COREi64/The-Phantom/Miniature Phantom by Tommi_nrw/C64 Userport Connections Reference.jpg

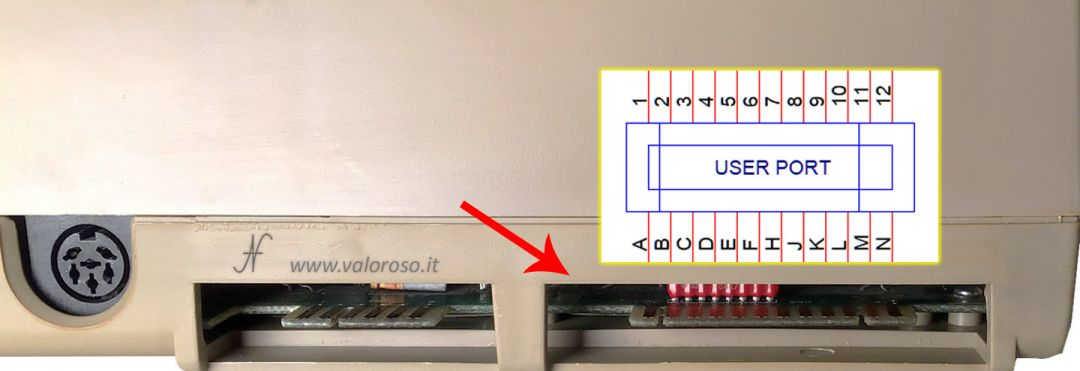
Miniature Phantom by Tommi_nrw/C64 Userport Connections Reference.jpg
