COREi64/The-Phantom/Miniature Phantom by Tommi_nrw/connections.jpg

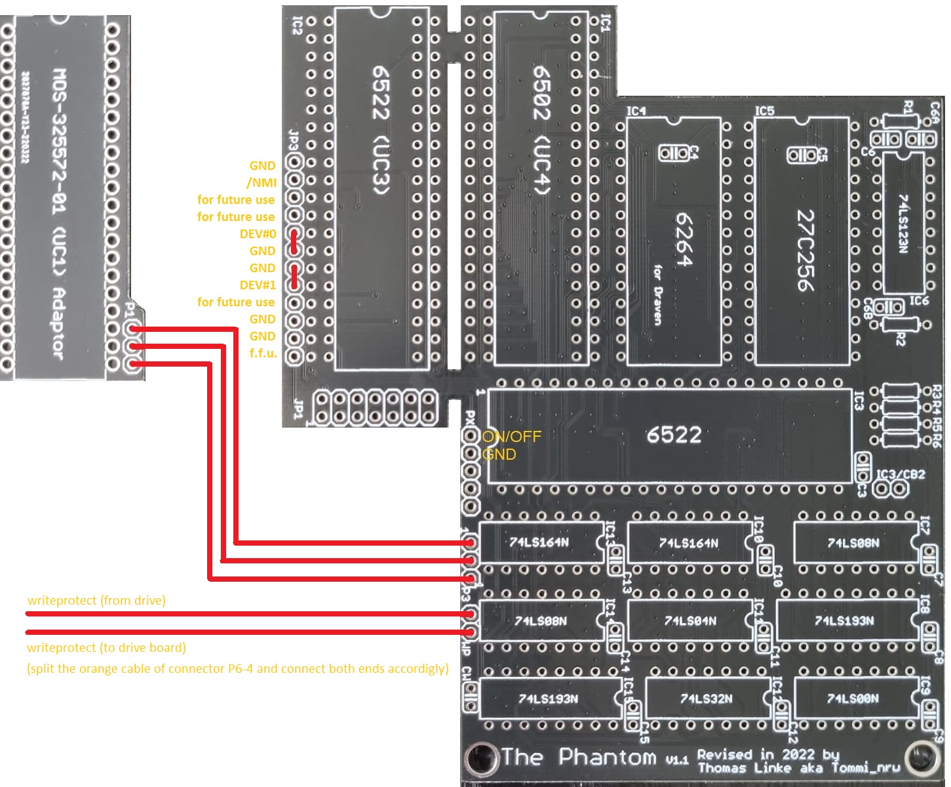
Miniature Phantom by Tommi_nrw/connections.jpg
