COREi64/The-Phantom/Miniature Phantom by Tommi_nrw/Gatearray-Adaptor.png

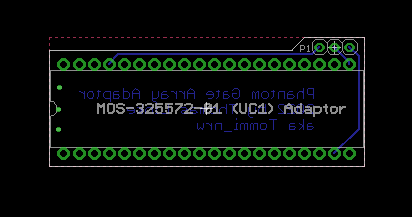
Miniature Phantom by Tommi_nrw/Gatearray-Adaptor.png
