COREi64/The-Phantom/Miniature Phantom by Tommi_nrw/Main PCB.png

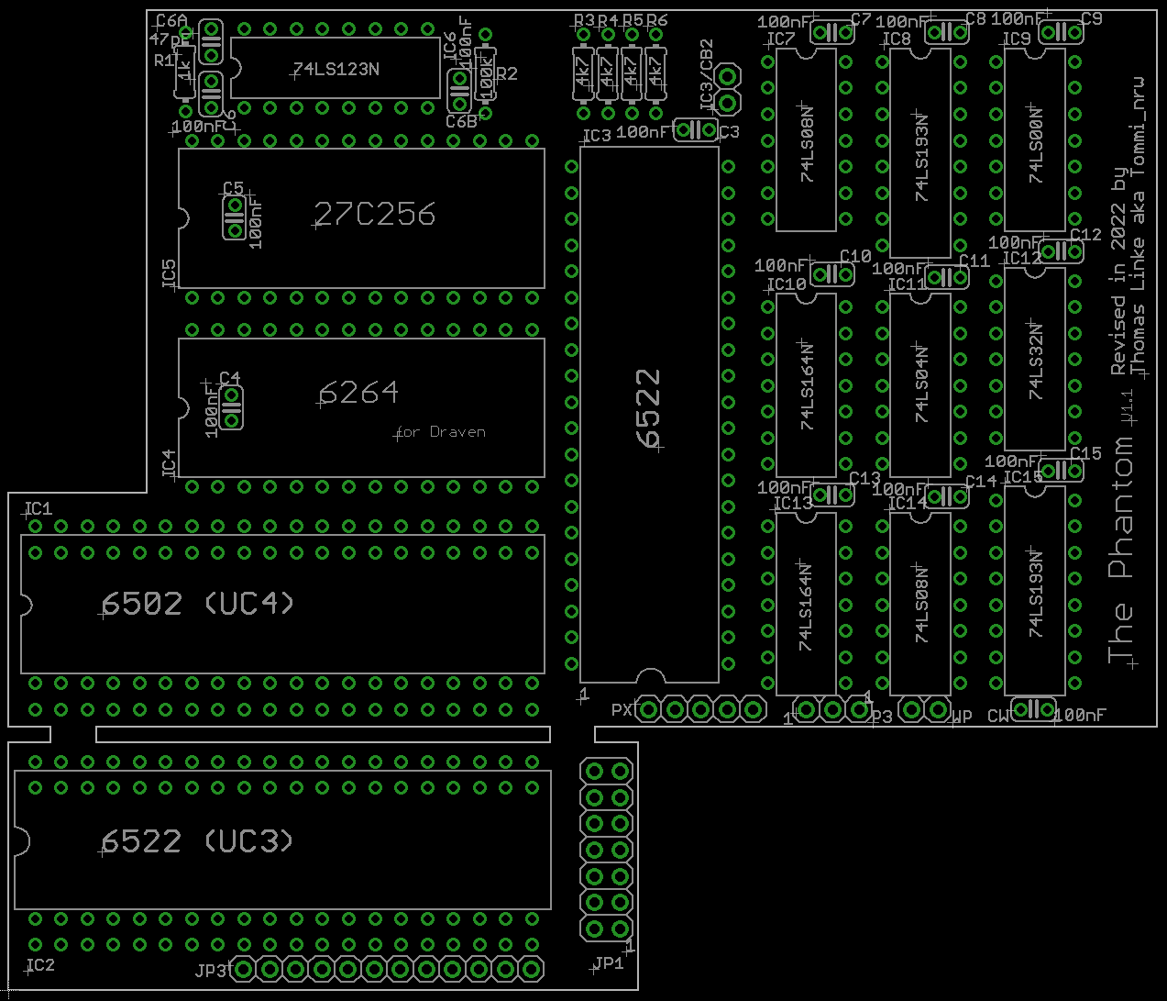
Miniature Phantom by Tommi_nrw/Main PCB.png
