COREi64/The-Phantom/Miniature Phantom by Tommi_nrw/Parallel cable.png

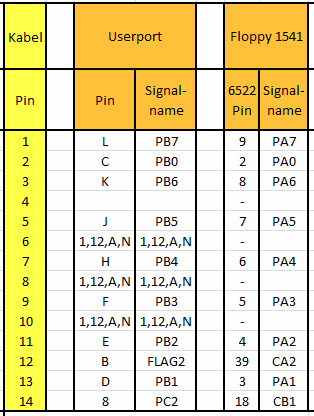
Miniature Phantom by Tommi_nrw/Parallel cable.png
