COREi64/The-Phantom/Miniature Phantom by Tommi_nrw/PCB connection.jpeg

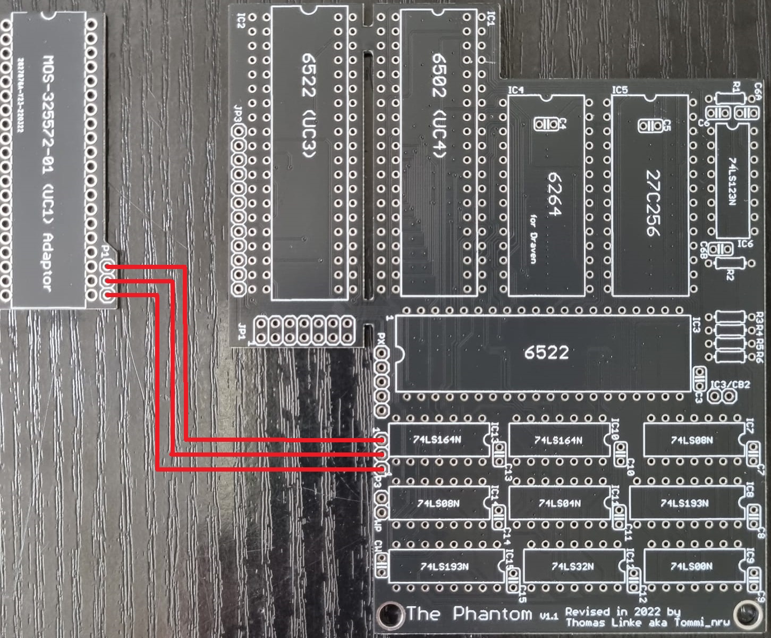
Miniature Phantom by Tommi_nrw/PCB connection.jpeg
