COREi64/The-Phantom/Miniature Phantom by Tommi_nrw/Phantom 1.1.jpeg

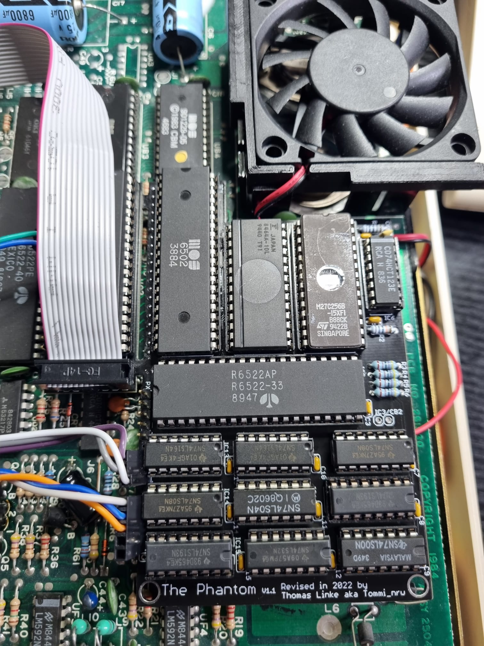
Miniature Phantom by Tommi_nrw/Phantom 1.1.jpeg
