COREi64/The-Phantom/Miniature Phantom by Tommi_nrw/Speedtest.png

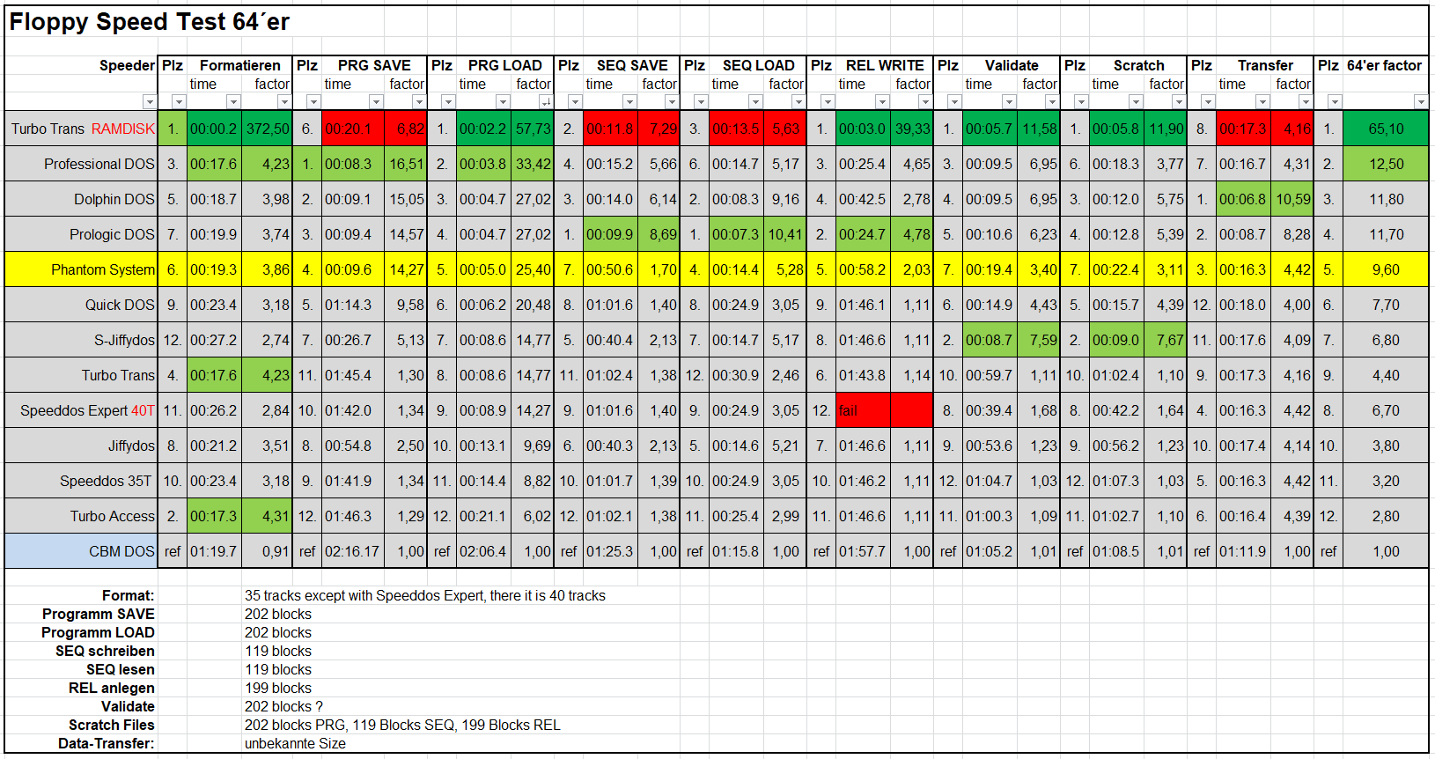
Miniature Phantom by Tommi_nrw/Speedtest.png
