COREi64/The-Phantom/Miniature Phantom by Tommi_nrw/userport-MAX.png

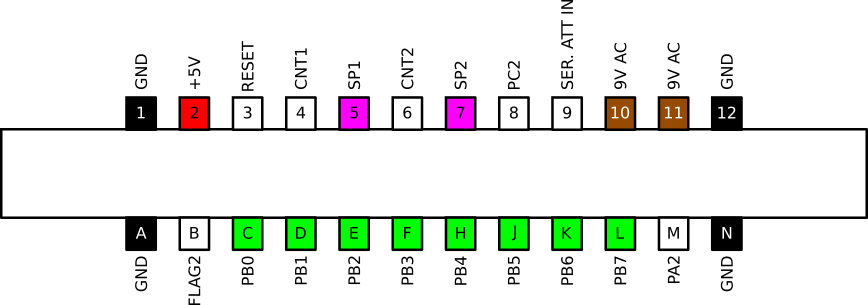
Miniature Phantom by Tommi_nrw/userport-MAX.png
