COREi64/The-Phantom/Photos/Advertisements/Phantom-AD-766x1024.jpg

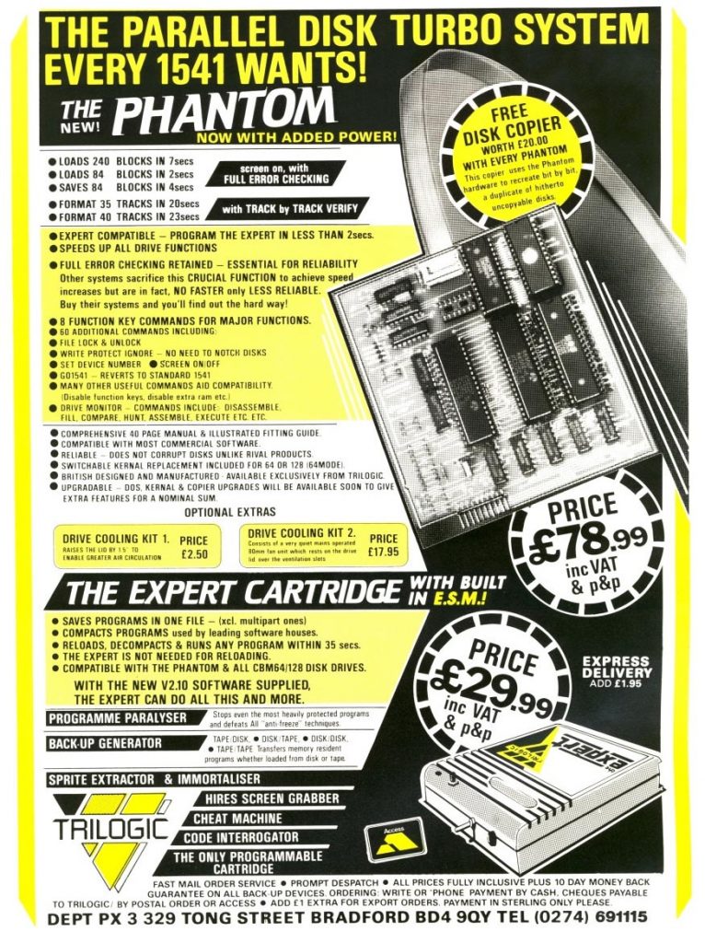
Photos/Advertisements/Phantom-AD-766x1024.jpg
