COREi64/The-Phantom/Build-it-Yourself Reference/Reference Photos/Parts Kit/2038.2021_06_27.JPG

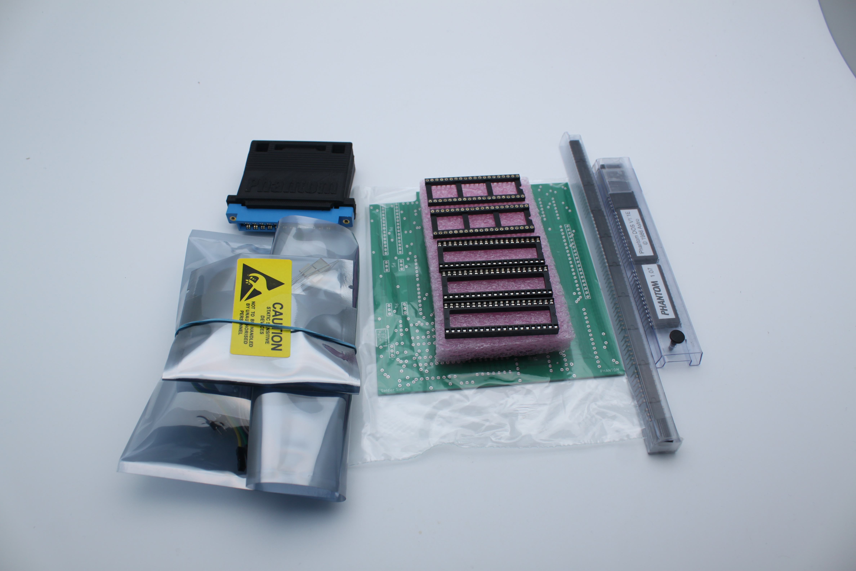
Build-it-Yourself Reference/Reference Photos/Parts Kit/2038.2021_06_27.JPG
