COREi64/The-Phantom/Build-it-Yourself Reference/Reference Photos/Finished Phantom Photos/1956.2021_06_18.JPG

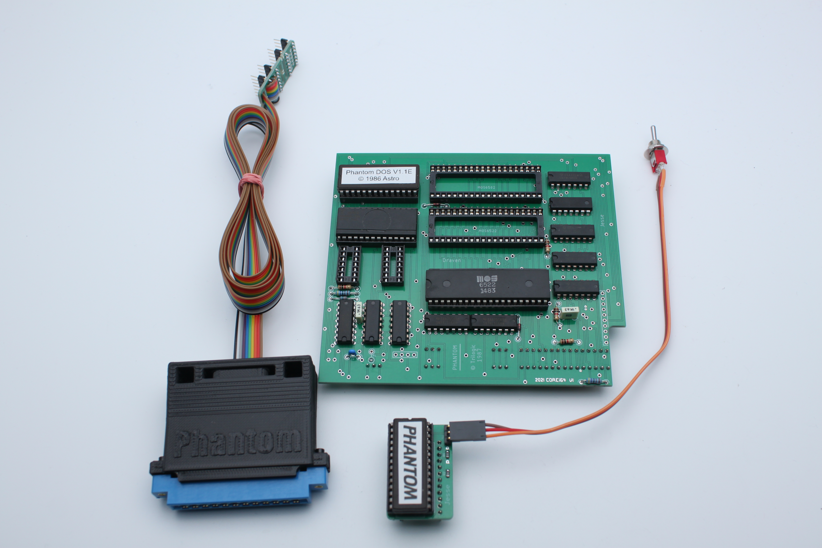
Build-it-Yourself Reference/Reference Photos/Finished Phantom Photos/1956.2021_06_18.JPG
