COREi64/The-Phantom/Build-it-Yourself Reference/Reference Photos/Finished Phantom Photos/1977.2021_06_22.JPG

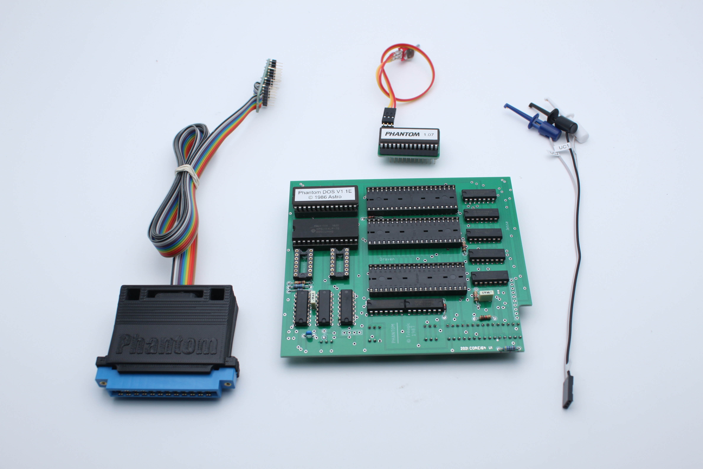
Build-it-Yourself Reference/Reference Photos/Finished Phantom Photos/1977.2021_06_22.JPG
