COREi64/The-Phantom/Build-it-Yourself Reference/Reference Photos/Parallel Userport Cable/1920.2021_06_09.JPG

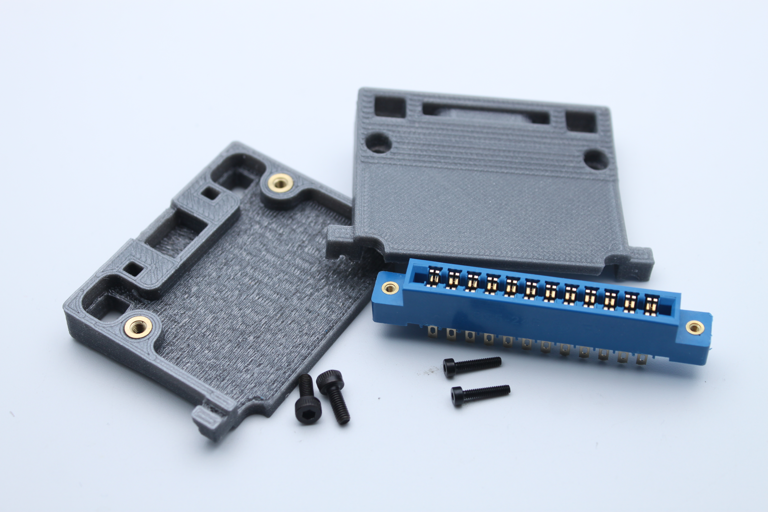
Build-it-Yourself Reference/Reference Photos/Parallel Userport Cable/1920.2021_06_09.JPG
