COREi64/The-Phantom/Build-it-Yourself Reference/Reference Photos/Parallel Userport Cable/1940.2021_06_10.JPG

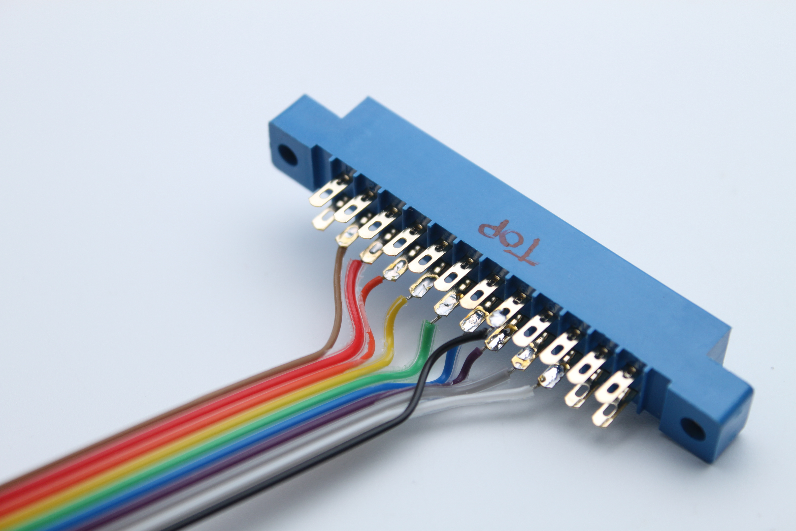
Build-it-Yourself Reference/Reference Photos/Parallel Userport Cable/1940.2021_06_10.JPG
