COREi64/The-Phantom/Build-it-Yourself Reference/Reference Photos/Parallel Userport Cable/1994.2021_06_22.JPG

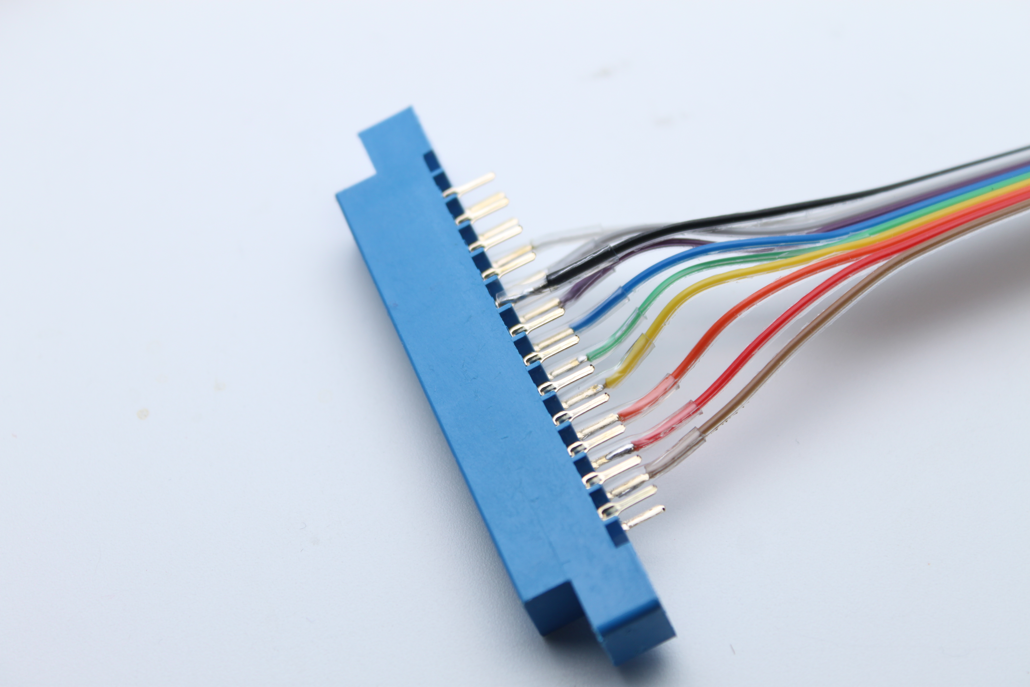
Build-it-Yourself Reference/Reference Photos/Parallel Userport Cable/1994.2021_06_22.JPG
