COREi64/The-Phantom/Build-it-Yourself Reference/Reference Photos/Parallel Userport Cable/2050.2021_06_27.JPG

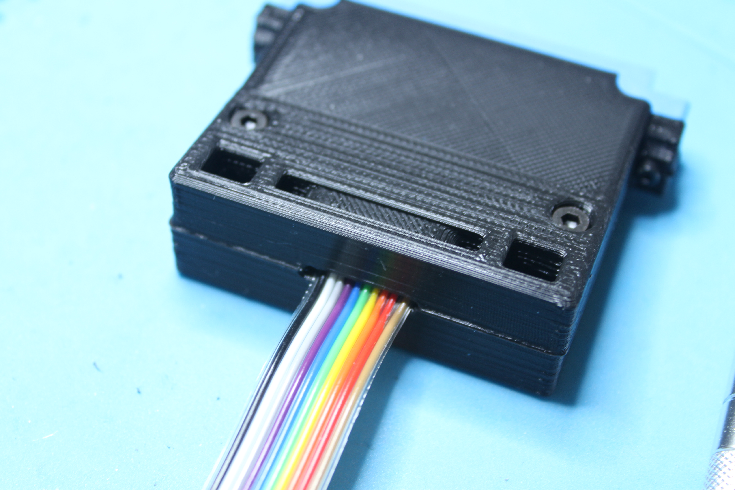
Build-it-Yourself Reference/Reference Photos/Parallel Userport Cable/2050.2021_06_27.JPG
