COREi64/The-Phantom/Build-it-Yourself Reference/Reference Photos/PCB Photos/1973.2021_06_18.JPG

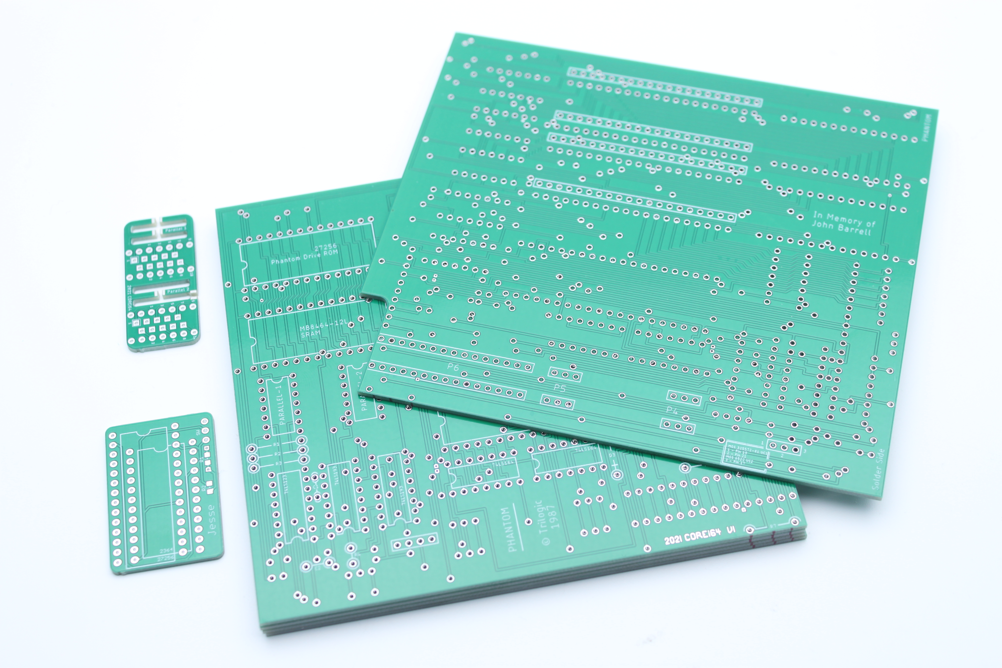
Build-it-Yourself Reference/Reference Photos/PCB Photos/1973.2021_06_18.JPG
