COREi64/The-Phantom/Build-it-Yourself Reference/Reference Photos/Phantom Drive Board/1985.2021_06_22.JPG

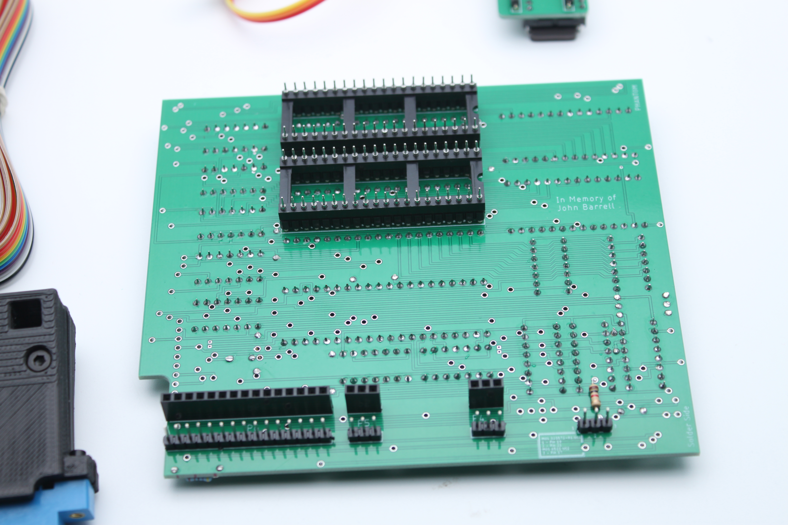
Build-it-Yourself Reference/Reference Photos/Phantom Drive Board/1985.2021_06_22.JPG
