COREi64/The-Phantom/Build-it-Yourself Reference/Reference Photos/Phantom Drive Board/2088.2021_06_28.JPG

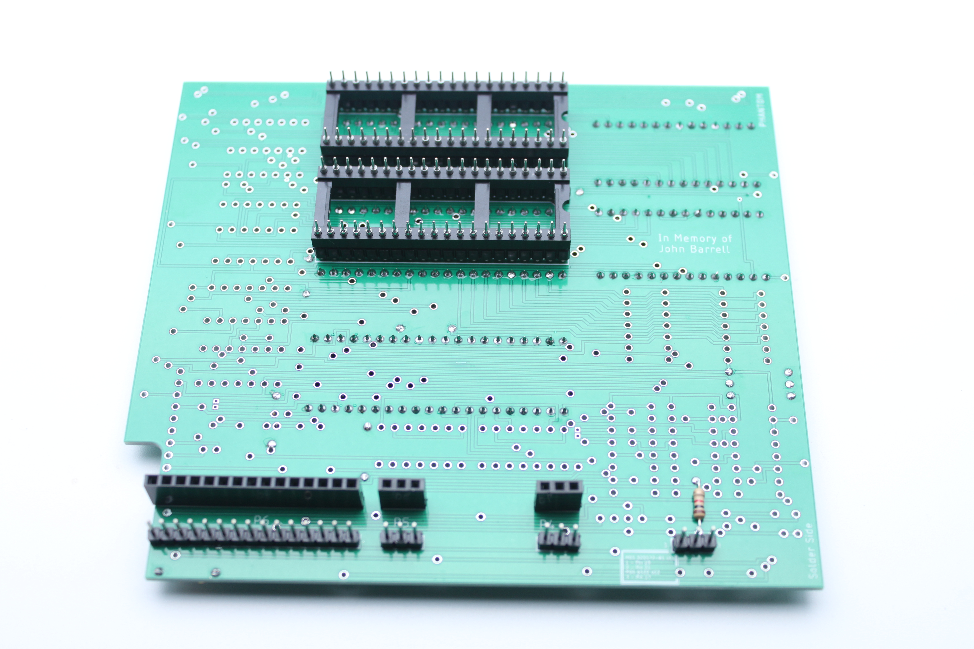
Build-it-Yourself Reference/Reference Photos/Phantom Drive Board/2088.2021_06_28.JPG
