COREi64/The-Phantom/Build-it-Yourself Reference/Reference Photos/Sync Clip/2055.2021_06_27.JPG

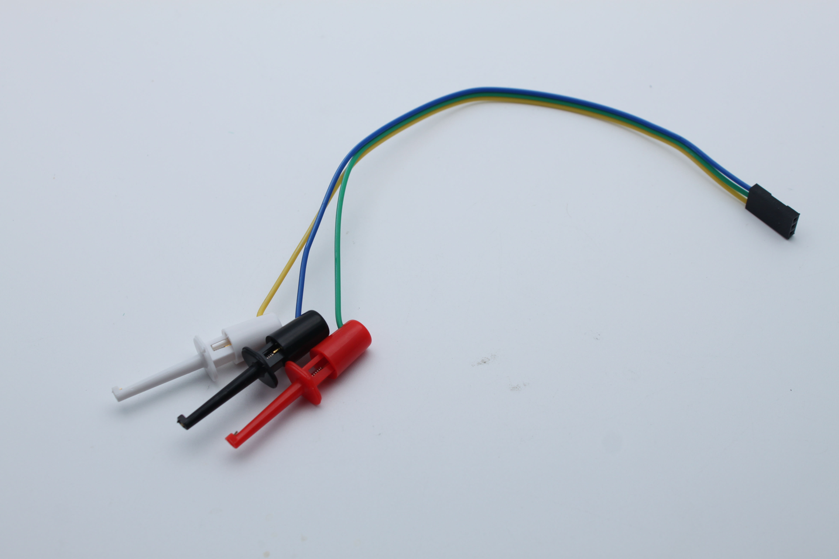
Build-it-Yourself Reference/Reference Photos/Sync Clip/2055.2021_06_27.JPG
