COREi64/The-Phantom/Photos/Original Installation Photos/Phantom-Board-1-1024x576.jpg

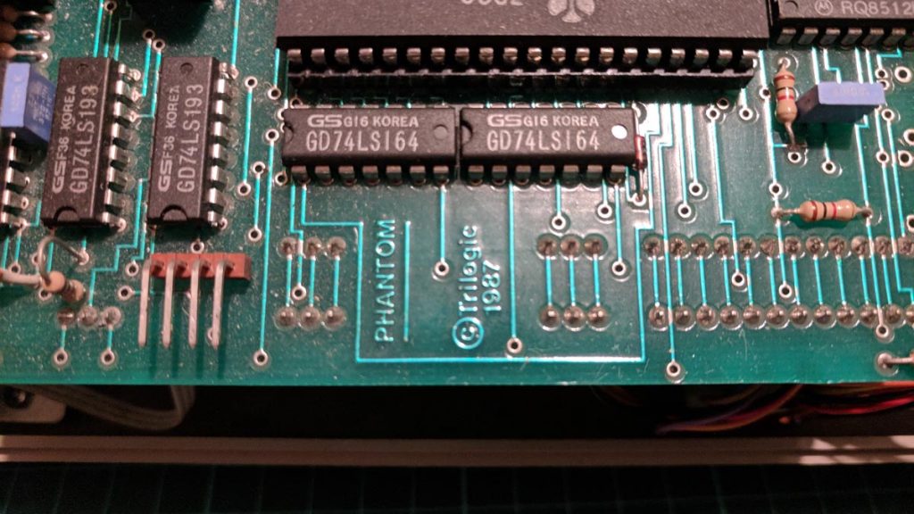
Photos/Original Installation Photos/Phantom-Board-1-1024x576.jpg
