COREi64/The-Phantom/Photos/Original Installation Photos/Phantom-cable-1-1024x684.jpg

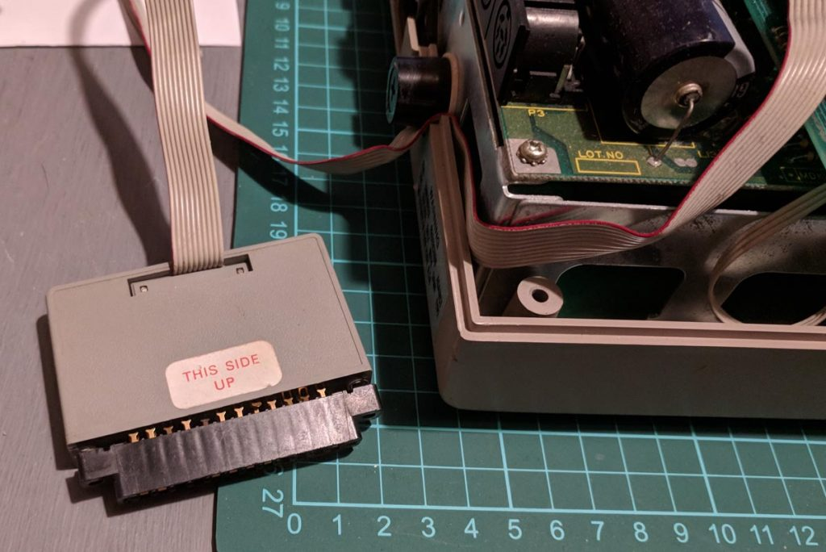
Photos/Original Installation Photos/Phantom-cable-1-1024x684.jpg
