COREi64/The-Phantom/Photos/Pre-Deconstruction Photos/1610.2021_04_20.JPG

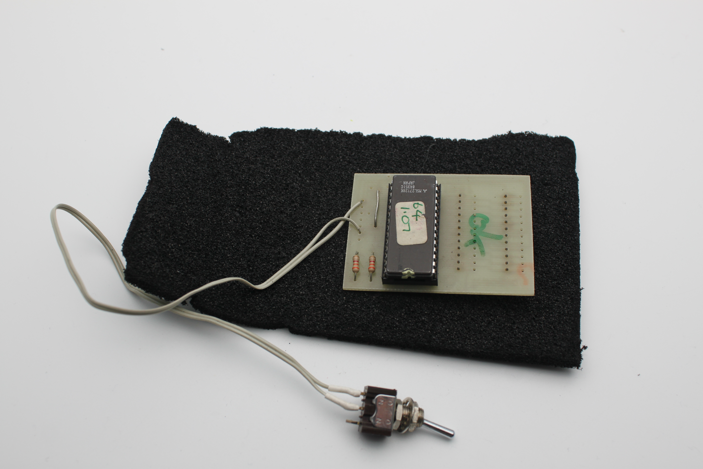
Photos/Pre-Deconstruction Photos/1610.2021_04_20.JPG
