COREi64/The-Phantom/Photos/Pre-Deconstruction Photos/1644.2021_04_24.JPG

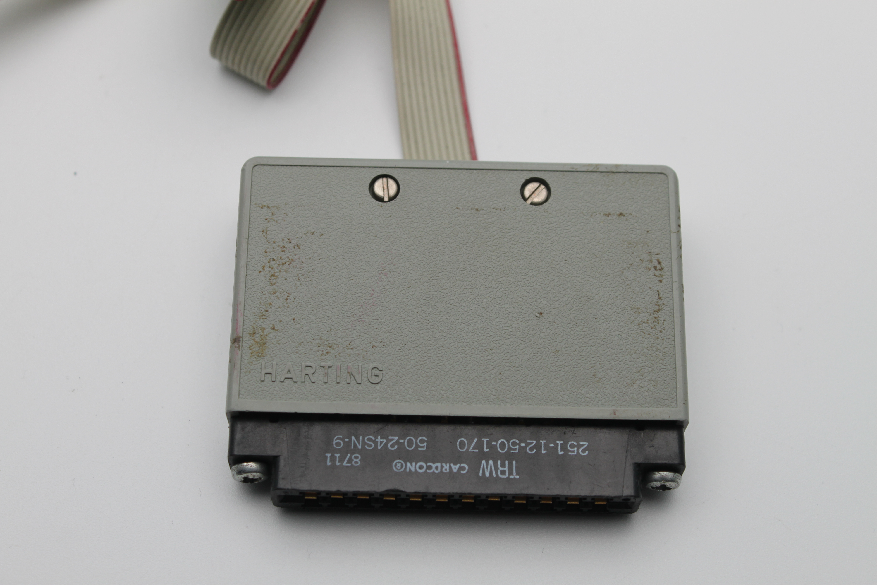
Photos/Pre-Deconstruction Photos/1644.2021_04_24.JPG
