COREi64/The-Phantom/Photos/Pre-Deconstruction Photos/1691.2021_04_24.JPG

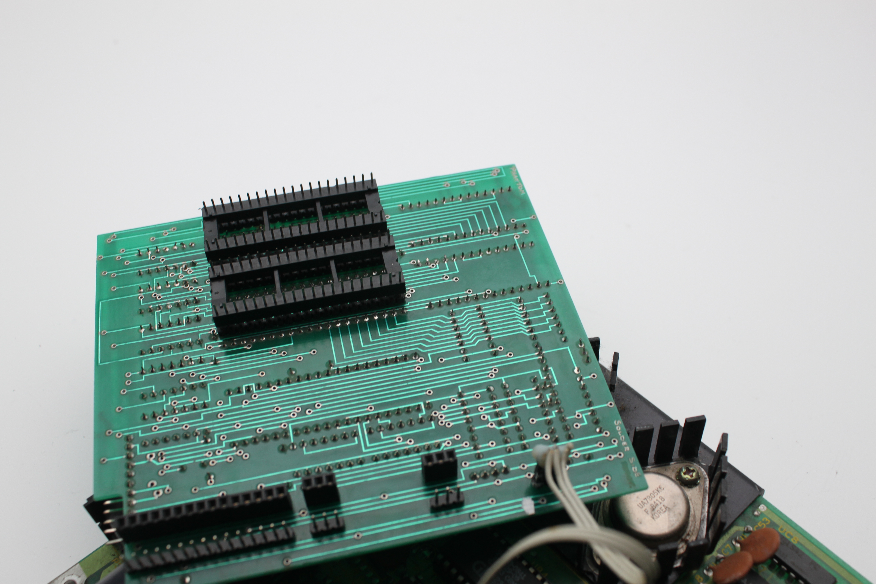
Photos/Pre-Deconstruction Photos/1691.2021_04_24.JPG
