COREi64/The-Phantom/Documentation/Expertise Issue 8-11 pg 4-5 Trilogic Phantom.jpg

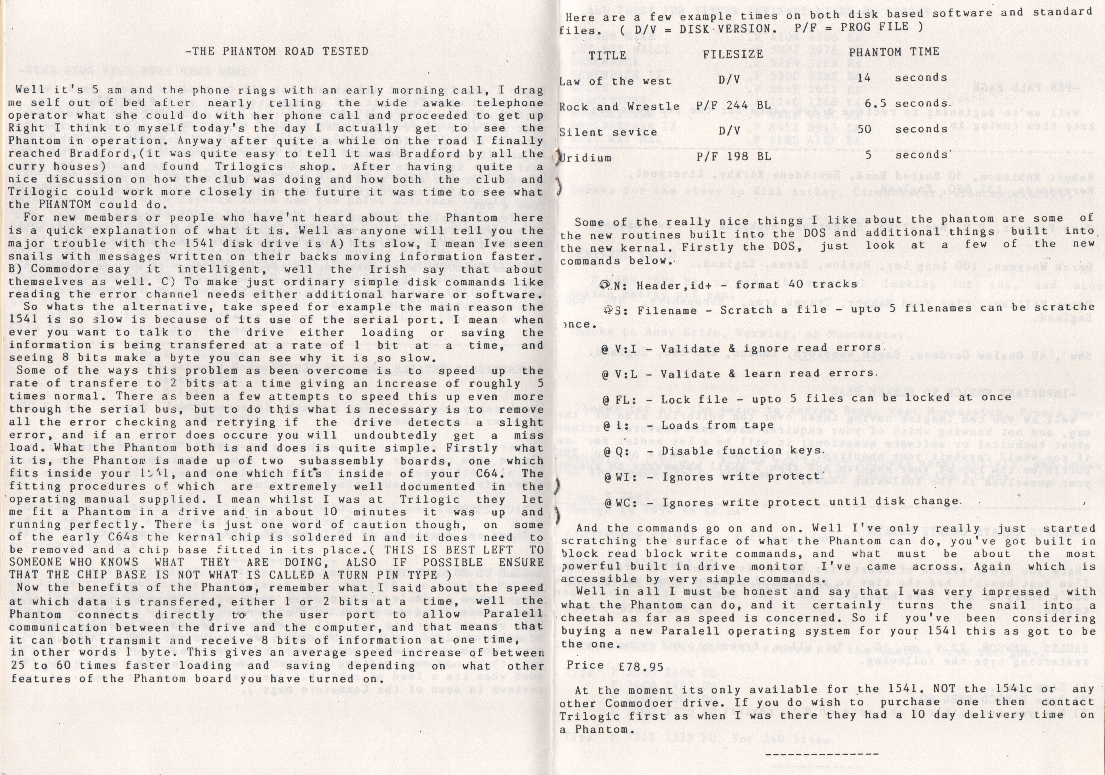
Documentation/Expertise Issue 8-11 pg 4-5 Trilogic Phantom.jpg
